pdp7/kicad-teensy-epaper/doc/lcd-assistant-dorkbotpdx.png

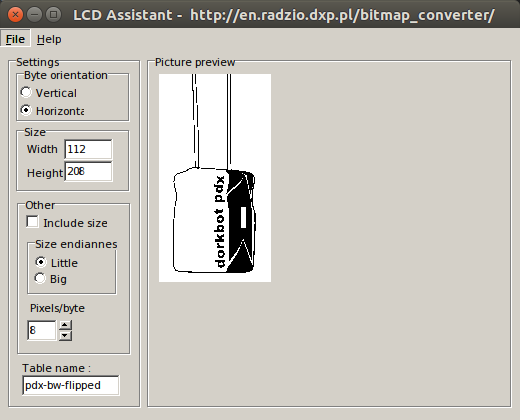
doc/lcd-assistant-dorkbotpdx.png
