pdp7/kicad-teensy-epaper/images/cvpcb.png

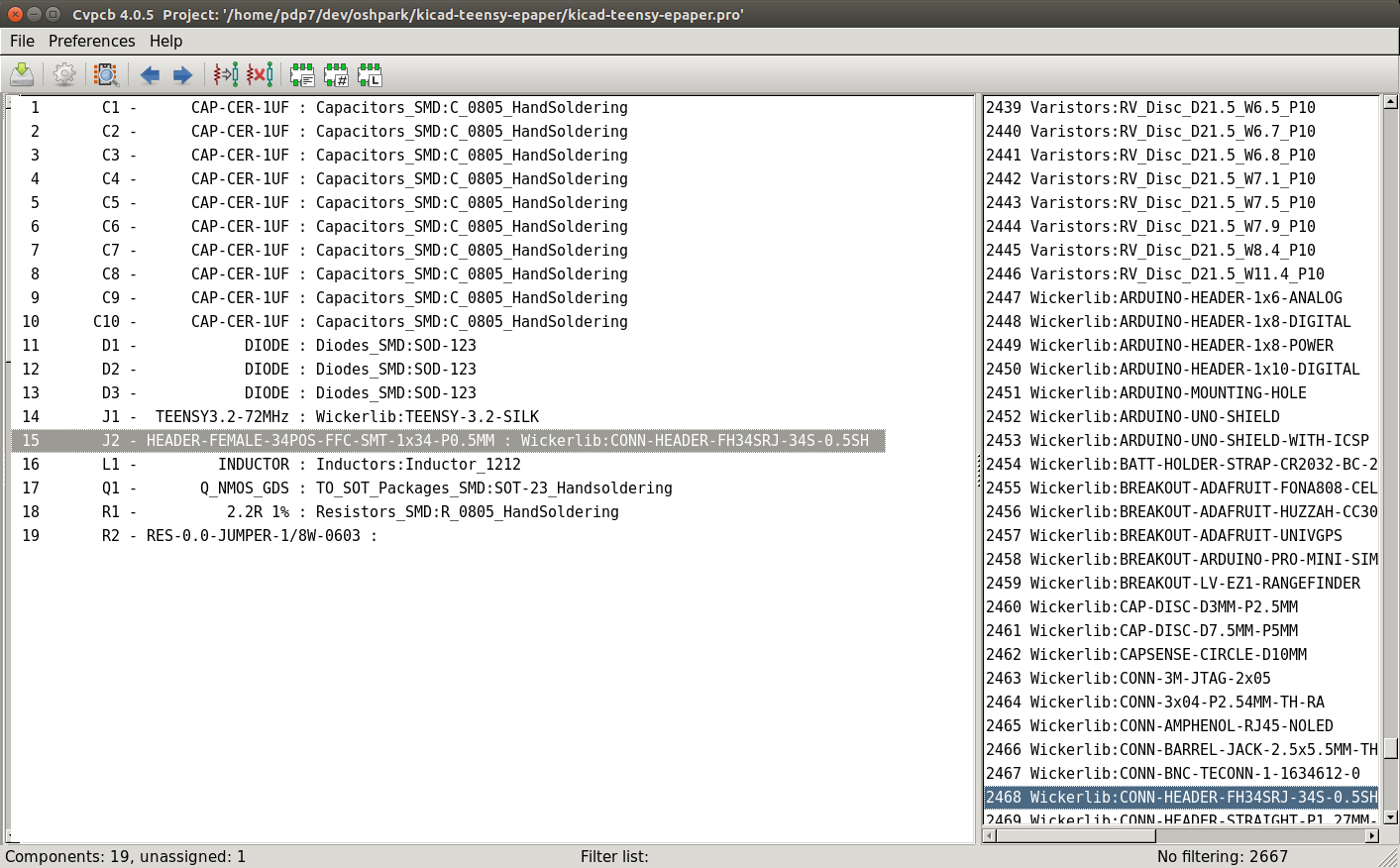
images/cvpcb.png
