pdp7/kicad-teensy-epaper/images/epaper-breakout-board-quotes.jpg

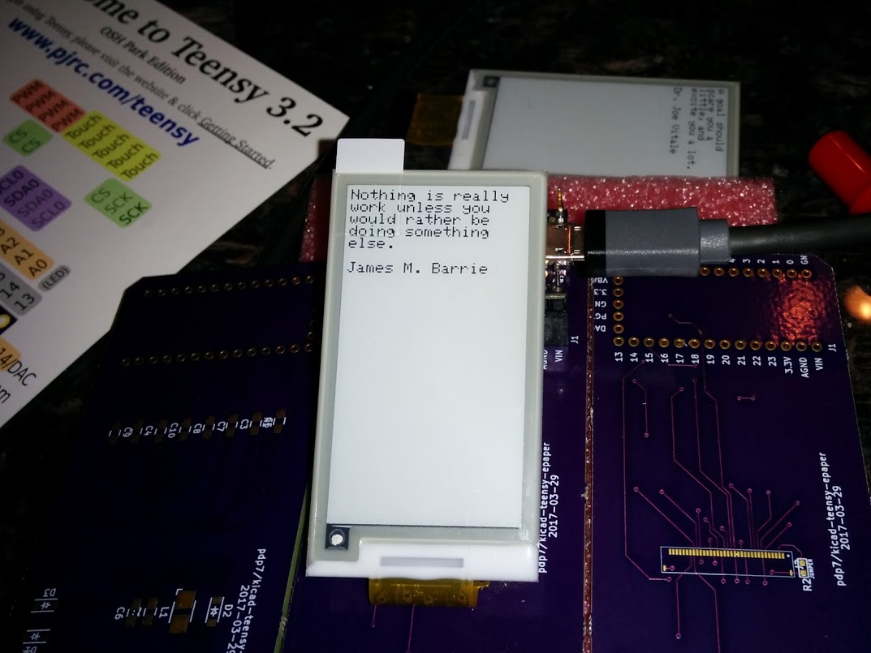
images/epaper-breakout-board-quotes.jpg
