pdp7/kicad-teensy-epaper/images/fancyepd/fancyepd-image-1.jpg

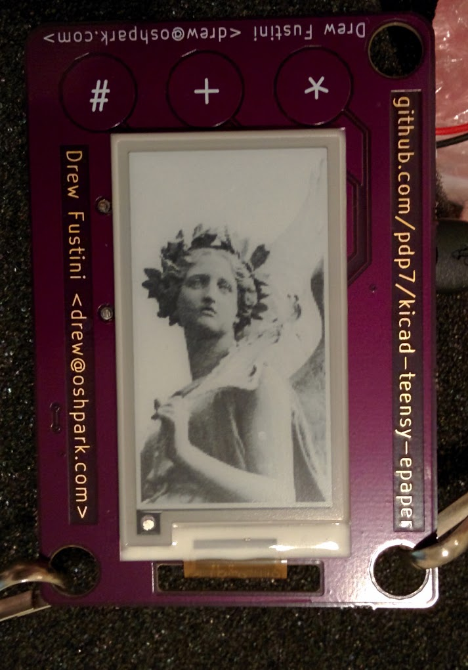
images/fancyepd/fancyepd-image-1.jpg
