pdp7/kicad-teensy-epaper/images/fancyepd/fancyepd-image-2.jpg

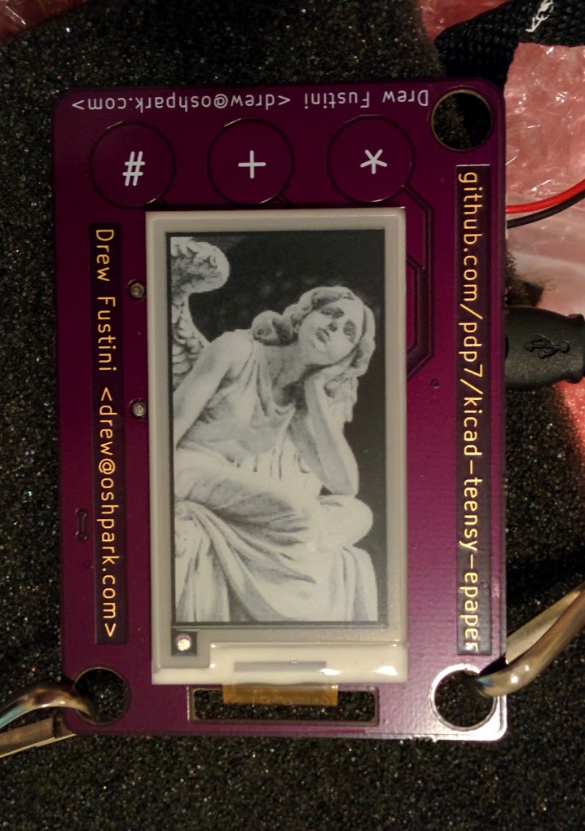
images/fancyepd/fancyepd-image-2.jpg
