pdp7/kicad-teensy-epaper/images/fancyepd/FancyEPDImageGenerator1.png

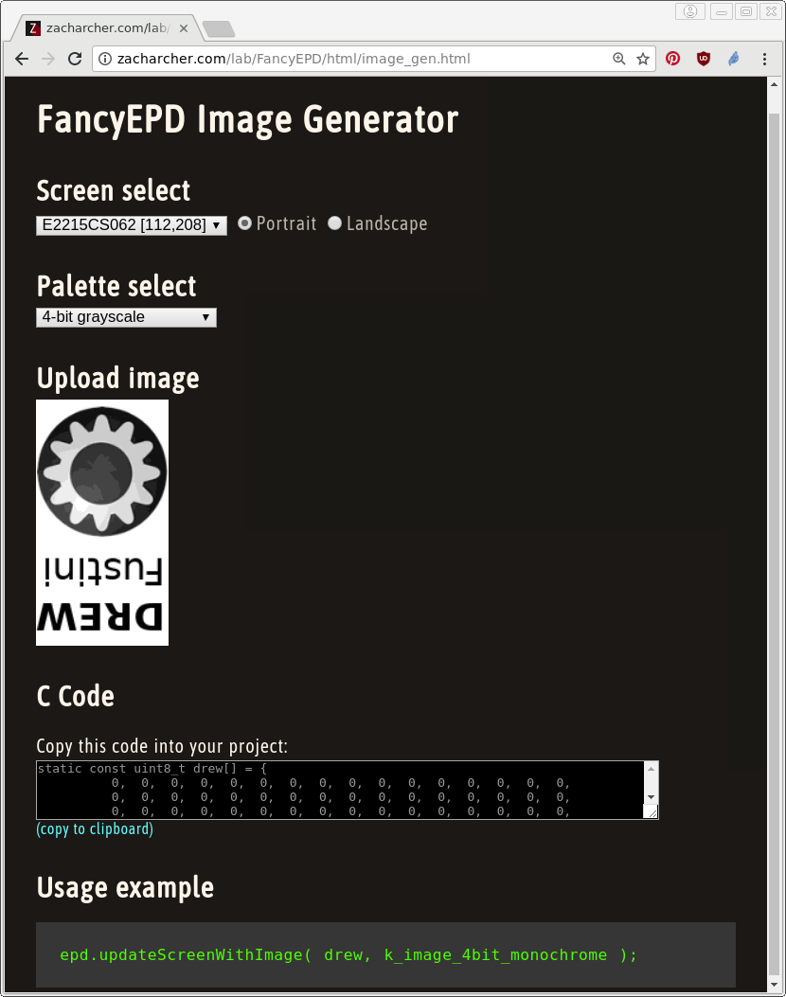
images/fancyepd/FancyEPDImageGenerator1.png
