pdp7/kicad-teensy-epaper/images/fpc-34pos-footprint.png

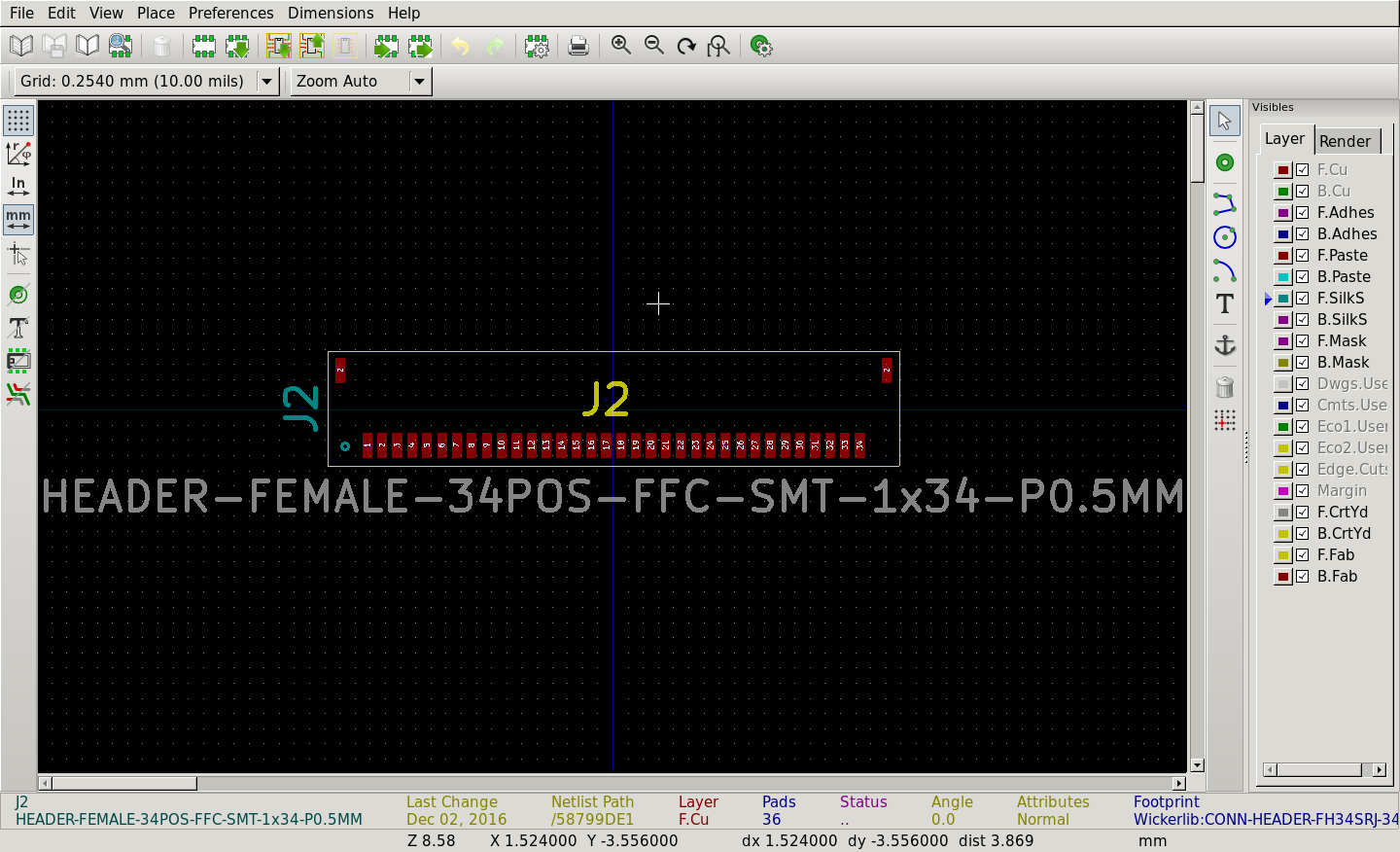
images/fpc-34pos-footprint.png
