pdp7/kicad-teensy-epaper/images/front-1.jpg

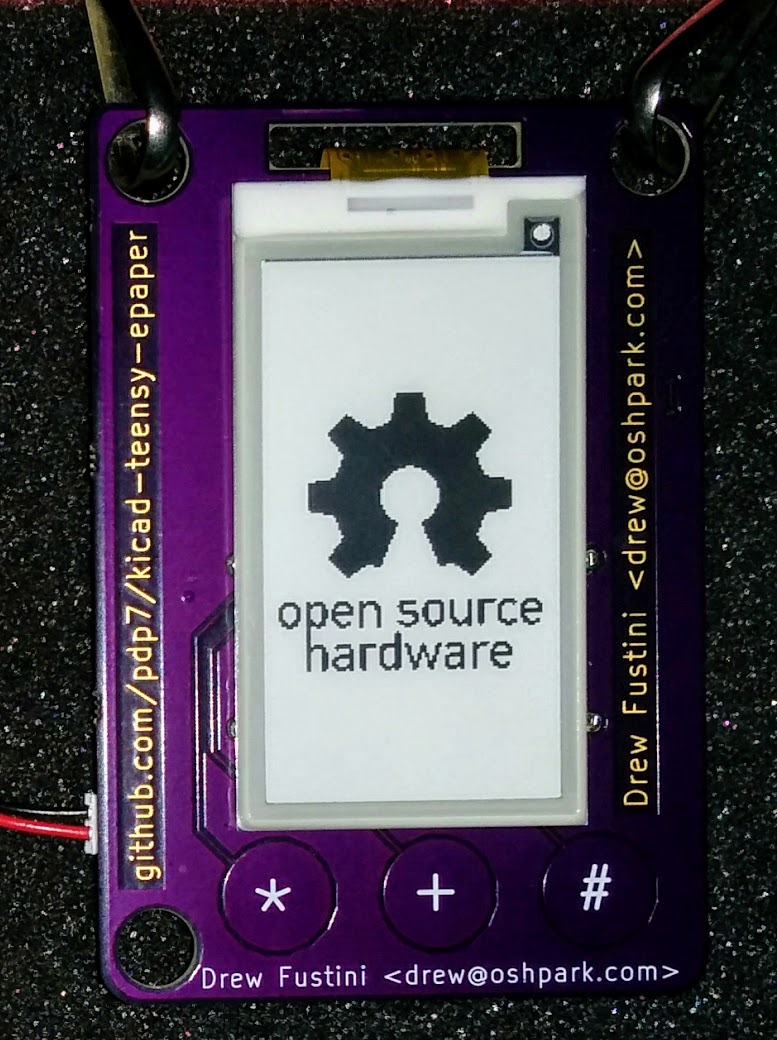
images/front-1.jpg
