pdp7/kicad-teensy-epaper/images/landscape.jpg

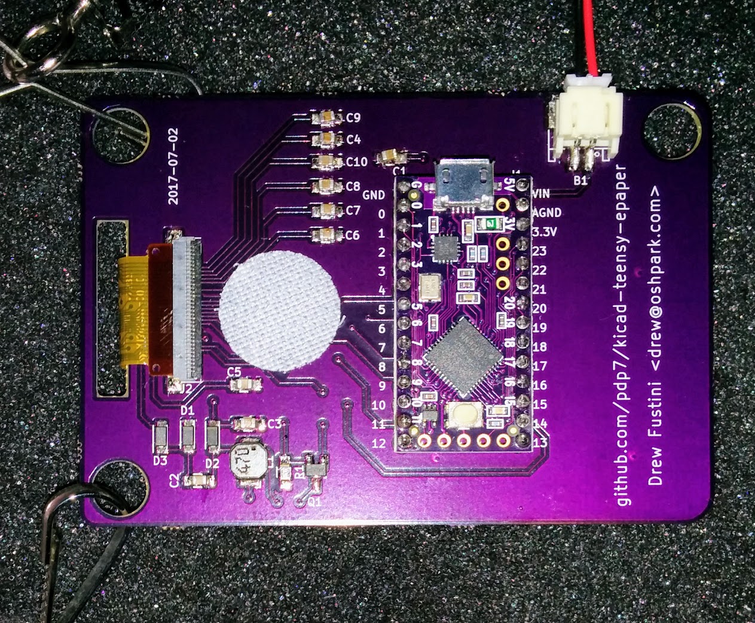
images/landscape.jpg
