pdp7/kicad-teensy-epaper/images/oshstencil.png

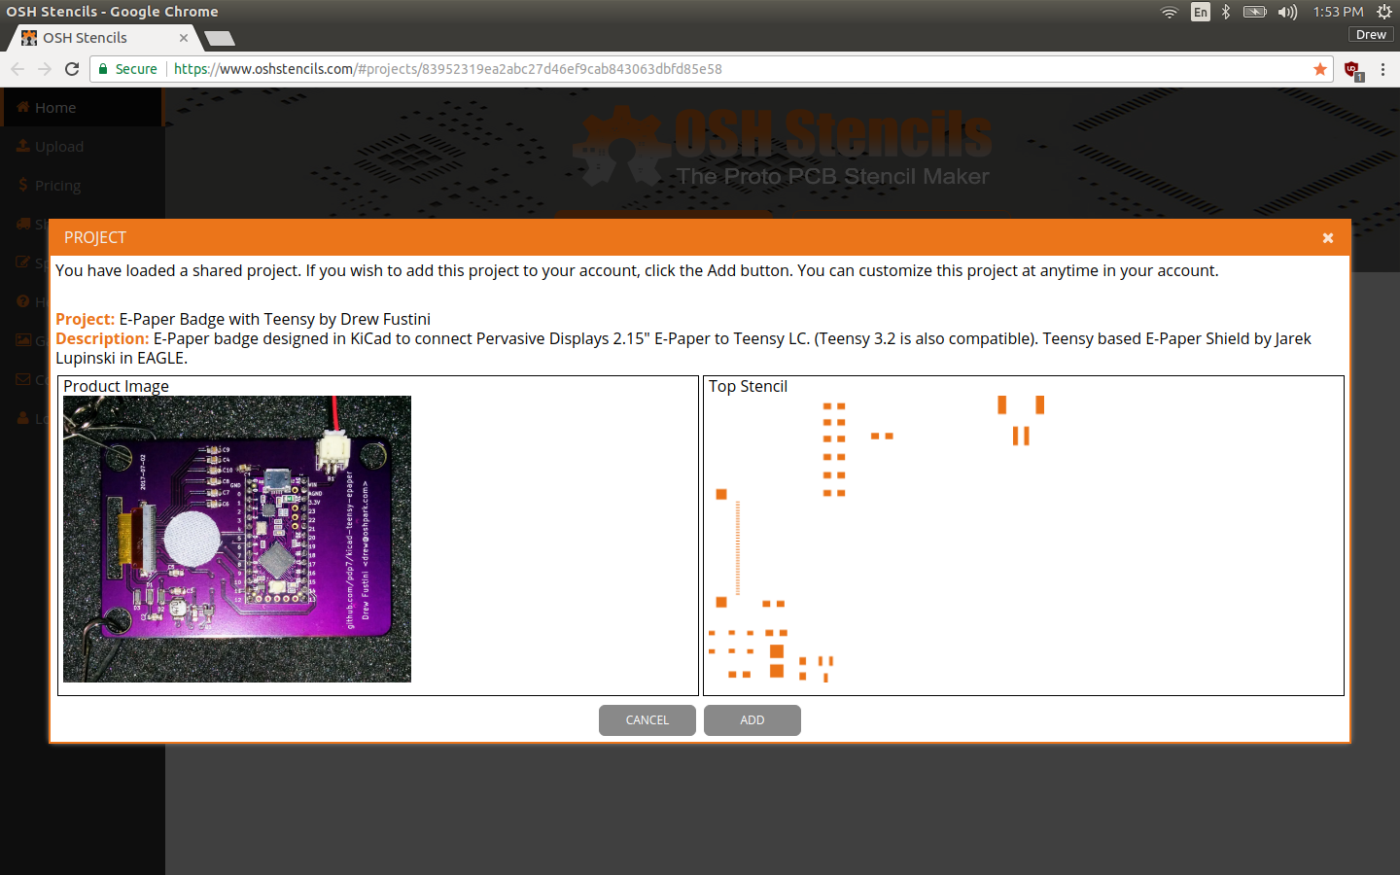
images/oshstencil.png
