pdp7/kicad-teensy-epaper/images/preview-bottom.png

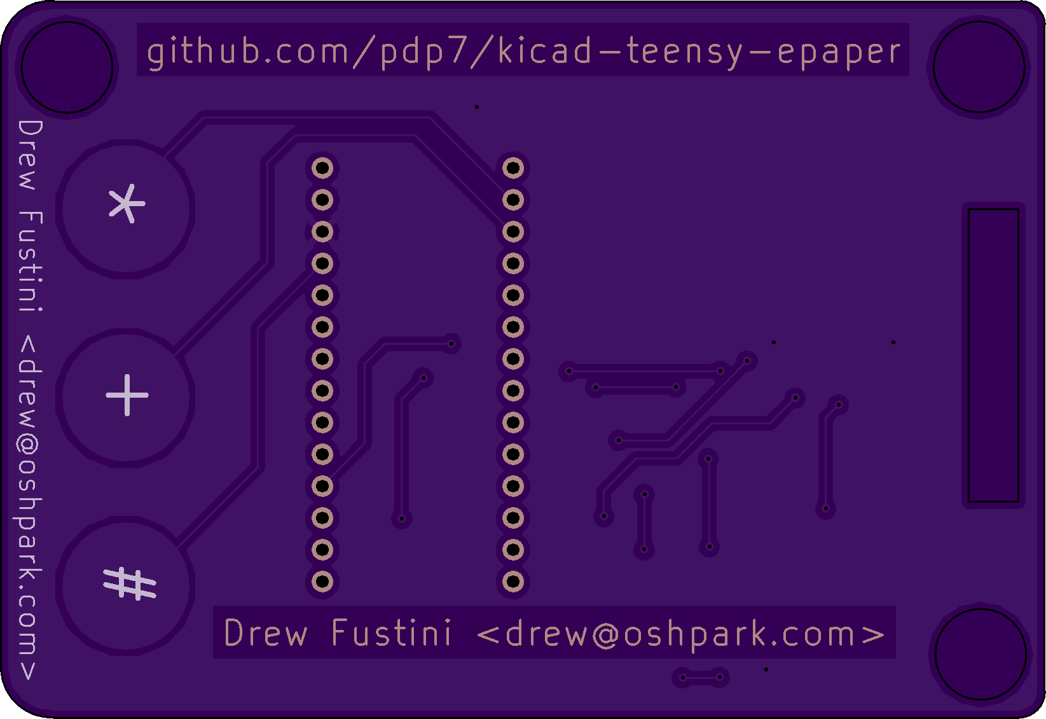
images/preview-bottom.png
