pdp7/kicad-teensy-epaper/tools/lcd-assistant-name.png

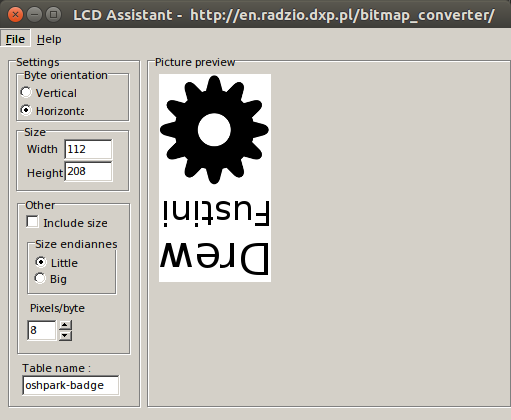
tools/lcd-assistant-name.png
