pdp7/kicad-teensy-epaper/images/kicad-epaper-digikey-bom.png

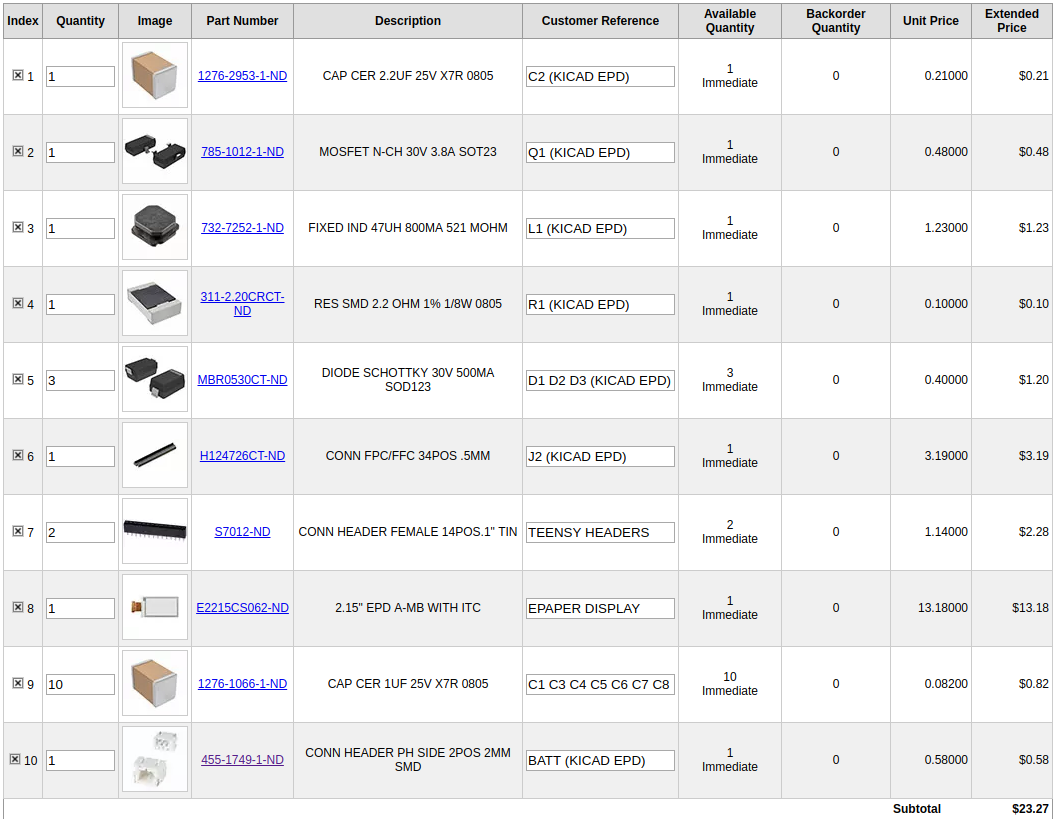
images/kicad-epaper-digikey-bom.png
